kaanaksoy/ESPing/esping/credentials_example.h

#ifndef CREDENTIALS_H
#define CREDENTIALS_H

/**************************************************************************/
/*!
    @file     credentials_example.h
    @brief    Header file for credentials

    @details  Contains credentials for the project.
    @note     This file is not used in the project, it is only an example.

    HOW TO USE:
    - Create a new file called credentials.h
    - Copy the contents of this file into credentials.h
    - Replace the credentials with your own
*/
/**************************************************************************/

// WiFi credentials
#define WIFI_SSID "Your_WiFi_SSID"
#define WIFI_PASSWORD "Your_WiFi_Password"

// MQTT credentials
#define MQTT_SERVER "192.168.1.xxx"
#define MQTT_PORT 1883 // Default port for MQTT
#define MQTT_USER "your_username"
#define MQTT_PASSWORD "your_password"

#endif
